FaBoPlatform/GameFive/firmware/doom/main/i_sound.c

/*
 * Game Five DOOM — sound layer: 8-channel SFX mixer + OPL2 music
 * -> MAX98357A over I2S
 *
 * PrBoom: Copyright (C) 1999-2006 id Software, Lee Killough, Colin Phipps
 * et al., GPL-2.0. Game Five I2S implementation 2026.
 *
 * SFX: DMX-format lumps are read zero-copy from the memory-mapped WAD
 * partition and resampled by a 16.16 stepper into the mix.
 * Music: MUS lump -> MIDI (mus2mid) -> prboom-plus opl_synth_player
 * (DBOPL OPL2 emulator, components/oplmusic) rendered synchronously in
 * the same mixer task on core 1.
 *
 * The I2S LRCLK MUST be a MAX98357A-supported rate (8/16/32/44.1/48 kHz).
 * 11025 Hz is NOT in the amp's supported list — its clock monitor mutes
 * the output entirely (this was why the first revision made no sound).
 * We run everything at 32 kHz and let the steppers resample.
 */

#include "config.h"
#include <string.h>
#include <stdio.h>
#include <stdlib.h>
#include "doomdef.h"
#include "doomstat.h"
#include "doomtype.h"
#include "sounds.h"
#include "s_sound.h"
#include "i_sound.h"
#include "w_wad.h"
#include "lprintf.h"
#include "memio.h"
#include "mus2mid.h"
#include "musicplayer.h"

#include "freertos/FreeRTOS.h"
#include "freertos/task.h"
#include "freertos/semphr.h"
#include "driver/i2s_std.h"
#include "esp_cpu.h"

#include "doom_config.h"

extern const music_player_t opl_synth_player;

int snd_card = 1;        /* sfx enabled */
int mus_card = 1;        /* OPL2 music */
int snd_samplerate = 32000;
int mus_opl_gain = 50;   /* used by oplmusic/opl.c FillBuffer */

#define MIX_RATE     32000        /* MAX98357A-supported LRCLK */
#define MIX_FRAMES   256          /* 8 ms per block at 32 kHz */
#define NUM_CHANNELS 16
#define MASTER_SHIFT 2            /* s(-128..127)*vol(0..127)>>2 ≈ -12dBFS/ch */

typedef struct {
    const uint8_t *data;   /* unsigned 8-bit samples (mmapped flash) */
    uint32_t len;          /* sample count */
    uint32_t pos;          /* 16.16 fixed */
    uint32_t step;         /* 16.16 fixed: lump rate / MIX_RATE */
    int vol;               /* 0..127 */
    volatile int active;
} mix_chan_t;

static mix_chan_t chans[NUM_CHANNELS];
static portMUX_TYPE snd_mux = portMUX_INITIALIZER_UNLOCKED;
static i2s_chan_handle_t s_tx;
static int snd_inited;

/* ---- music state (guarded by mus_lock: API calls come from the doom
 * task on core 0, rendering happens in the sound task on core 1) ---- */
static SemaphoreHandle_t mus_lock;
static int mus_inited;
static const void *mus_handle;
static void *mus_mididata;         /* converted MIDI buffer (heap) */
static volatile int mus_playing;

static void sound_task(void *arg)
{
    static int16_t buf[MIX_FRAMES * 2];  /* L+R interleaved */
    static int16_t mbuf[MIX_FRAMES * 2]; /* music render block */
    uint32_t prof_cycles = 0, prof_blocks = 0;

    for (;;) {
        uint32_t c0 = esp_cpu_get_cycle_count();

        /* music first: OPL render into its own block */
        int have_music = 0;
        if (mus_inited && xSemaphoreTake(mus_lock, 0) == pdTRUE) {
            if (mus_playing) {
                opl_synth_player.render(mbuf, MIX_FRAMES);
                have_music = 1;
            }
            xSemaphoreGive(mus_lock);
        }

        for (int i = 0; i < MIX_FRAMES; i++) {
            int32_t mix = have_music ? mbuf[i * 2] : 0;
            taskENTER_CRITICAL(&snd_mux);
            for (int c = 0; c < NUM_CHANNELS; c++) {
                mix_chan_t *ch = &chans[c];
                if (!ch->active)
                    continue;
                uint32_t idx = ch->pos >> 16;
                if (idx >= ch->len) {
                    ch->active = 0;
                    continue;
                }
                mix += (((int)ch->data[idx] - 128) * ch->vol) >> MASTER_SHIFT;
                ch->pos += ch->step;
            }
            taskEXIT_CRITICAL(&snd_mux);
            if (mix > 32767) mix = 32767;
            if (mix < -32768) mix = -32768;
            buf[i * 2] = (int16_t)mix;
            buf[i * 2 + 1] = (int16_t)mix;
        }

        prof_cycles += esp_cpu_get_cycle_count() - c0;
        if (++prof_blocks == 1250) {   /* ~10 s of blocks */
            /* budget per block: 8 ms * 240 MHz = 1.92 Mcycles */
            lprintf(LO_INFO, "sound_task: avg %u cyc/block (budget 1920000)\n",
                    (unsigned)(prof_cycles / prof_blocks));
            prof_cycles = prof_blocks = 0;
        }

        size_t written;
        esp_err_t err =
            i2s_channel_write(s_tx, buf, sizeof(buf), &written, portMAX_DELAY);
        static int dbg_state; /* 0=init, 1=reported nonzero, <0=reported err */
        if (err != ESP_OK && dbg_state >= 0) {
            dbg_state = -1;
            lprintf(LO_WARN, "sound_task: i2s write err 0x%x\n", err);
        } else if (dbg_state == 0 && buf[0] != 0) {
            dbg_state = 1;
            lprintf(LO_INFO, "sound_task: first nonzero audio block\n");
        }
    }
}

void I_InitSound(void)
{
    if (snd_inited)
        return;

    i2s_chan_config_t ccfg =
        I2S_CHANNEL_DEFAULT_CONFIG(I2S_NUM_AUTO, I2S_ROLE_MASTER);
    if (i2s_new_channel(&ccfg, &s_tx, NULL) != ESP_OK) {
        lprintf(LO_WARN, "I_InitSound: i2s channel alloc failed\n");
        snd_card = 0;
        mus_card = 0;
        return;
    }
    i2s_std_config_t scfg = {
        .clk_cfg = I2S_STD_CLK_DEFAULT_CONFIG(MIX_RATE),
        .slot_cfg = I2S_STD_PHILIPS_SLOT_DEFAULT_CONFIG(
            I2S_DATA_BIT_WIDTH_16BIT, I2S_SLOT_MODE_STEREO),
        .gpio_cfg = {
            .mclk = I2S_GPIO_UNUSED,
            .bclk = 6,   /* GF_PIN_I2S_BCLK  (XIAO D5) */
            .ws   = 43,  /* GF_PIN_I2S_LRCLK (XIAO D6) */
            .dout = 44,  /* GF_PIN_I2S_DIN   (XIAO D7) */
            .din  = I2S_GPIO_UNUSED,
        },
    };
    if (i2s_channel_init_std_mode(s_tx, &scfg) != ESP_OK ||
        i2s_channel_enable(s_tx) != ESP_OK) {
        lprintf(LO_WARN, "I_InitSound: i2s init failed\n");
        snd_card = 0;
        mus_card = 0;
        return;
    }

    mus_lock = xSemaphoreCreateMutex();
    I_InitMusic();

    xTaskCreatePinnedToCore(sound_task, "sound", 8192, NULL, 6, NULL, 1);
    snd_inited = 1;
    lprintf(LO_INFO, "I_InitSound: I2S %d Hz, %d mix channels, music=%s\n",
            MIX_RATE, NUM_CHANNELS, mus_inited ? "OPL2" : "off");
}

void I_ShutdownSound(void)
{
}

void I_SetChannels(void)
{
}

int I_GetSfxLumpNum(sfxinfo_t *sfx)
{
    char namebuf[9];
    snprintf(namebuf, sizeof(namebuf), "ds%.6s", sfx->name);
    return W_CheckNumForName(namebuf);
}

/*
 * DMX lump: u16 format(=3), u16 rate, u32 length, then `length` unsigned
 * 8-bit samples of which the first/last 16 are padding.
 */
int I_StartSound(int id, int channel, int vol, int sep, int pitch,
                 int priority)
{
    if (!snd_inited || channel < 0 || channel >= NUM_CHANNELS)
        return -1;

    sfxinfo_t *sfx = &S_sfx[id];
    if (sfx->lumpnum < 0)
        sfx->lumpnum = I_GetSfxLumpNum(sfx);
    if (sfx->lumpnum < 0)
        return -1;

    const uint8_t *lump = W_CacheLumpNum(sfx->lumpnum);
    int lumplen = W_LumpLength(sfx->lumpnum);
    if (lump == NULL || lumplen < 8 + 32) {
        if (lump) W_UnlockLumpNum(sfx->lumpnum);
        return -1;
    }

    uint16_t fmt = lump[0] | (lump[1] << 8);
    uint16_t rate = lump[2] | (lump[3] << 8);
    uint32_t dlen = lump[4] | (lump[5] << 8) | (lump[6] << 16)
                    | ((uint32_t)lump[7] << 24);
    if (fmt != 3 || rate == 0) {
        W_UnlockLumpNum(sfx->lumpnum);
        return -1;
    }
    if (dlen > (uint32_t)(lumplen - 8))
        dlen = lumplen - 8;
    if (dlen <= 32) {
        W_UnlockLumpNum(sfx->lumpnum);
        return -1;
    }

    taskENTER_CRITICAL(&snd_mux);
    chans[channel].active = 0;
    chans[channel].data = lump + 8 + 16;   /* skip header + lead-in pad */
    chans[channel].len = dlen - 32;        /* drop both pads */
    chans[channel].pos = 0;
    chans[channel].step = ((uint32_t)rate << 16) / MIX_RATE;
    chans[channel].vol = vol < 0 ? 0 : (vol > 127 ? 127 : vol);
    chans[channel].active = 1;
    taskEXIT_CRITICAL(&snd_mux);

    static int dbg_count;
    if (dbg_count < 5) {
        dbg_count++;
        lprintf(LO_INFO, "I_StartSound: ds%.6s ch=%d vol=%d rate=%u len=%u\n",
                sfx->name, channel, vol, rate, (unsigned)(dlen - 32));
    }

    /* whole-partition mmap: the pointer stays valid after unlock */
    W_UnlockLumpNum(sfx->lumpnum);
    return channel;
}

void I_StopSound(int handle)
{
    if (handle < 0 || handle >= NUM_CHANNELS)
        return;
    taskENTER_CRITICAL(&snd_mux);
    chans[handle].active = 0;
    taskEXIT_CRITICAL(&snd_mux);
}

int I_SoundIsPlaying(int handle)
{
    if (handle < 0 || handle >= NUM_CHANNELS)
        return 0;
    return chans[handle].active != 0;
}

int I_AnySoundStillPlaying(void)
{
    for (int c = 0; c < NUM_CHANNELS; c++)
        if (chans[c].active)
            return 1;
    return 0;
}

void I_UpdateSoundParams(int handle, int volume, int seperation, int pitch)
{
    if (handle < 0 || handle >= NUM_CHANNELS)
        return;
    taskENTER_CRITICAL(&snd_mux);
    chans[handle].vol = volume < 0 ? 0 : (volume > 127 ? 127 : volume);
    taskEXIT_CRITICAL(&snd_mux);
}

/* ---- music: prboom-plus OPL2 synth (components/oplmusic) ---- */

void I_InitMusic(void)
{
    if (mus_inited || !mus_card)
        return;
    if (opl_synth_player.init(MIX_RATE)) {
        mus_inited = 1;
        lprintf(LO_INFO, "I_InitMusic: %s at %d Hz\n",
                opl_synth_player.name(), MIX_RATE);
    } else {
        mus_card = 0;
        lprintf(LO_WARN, "I_InitMusic: OPL init failed, music off\n");
    }
}

void I_ShutdownMusic(void)
{
}

/*
 * prboom hands us the raw lump (usually MUS, sometimes already MIDI).
 * Convert MUS -> standard MIDI in a heap buffer that must outlive the
 * song (the player parses it lazily); free it in I_UnRegisterSong.
 */
int I_RegisterSong(const void *data, size_t len)
{
    if (!mus_inited || data == NULL || len < 4)
        return 0;

    const void *mididata = data;
    size_t midilen = len;
    void *converted = NULL;

    if (memcmp(data, "MUS\x1a", 4) == 0) {
        MEMFILE *in = mem_fopen_read(data, len);
        MEMFILE *out = mem_fopen_write();
        if (in == NULL || out == NULL || mus2mid(in, out)) {
            lprintf(LO_WARN, "I_RegisterSong: MUS->MIDI conversion failed\n");
            if (in) mem_fclose(in);
            if (out) mem_fclose(out);
            return 0;
        }
        void *outbuf;
        size_t outlen;
        mem_get_buf(out, &outbuf, &outlen);
        converted = malloc(outlen);
        if (converted == NULL) {
            mem_fclose(in);
            mem_fclose(out);
            return 0;
        }
        memcpy(converted, outbuf, outlen);
        mididata = converted;
        midilen = outlen;
        mem_fclose(in);
        mem_fclose(out);
    }

    xSemaphoreTake(mus_lock, portMAX_DELAY);
    if (mus_handle) {                       /* stale song still registered */
        opl_synth_player.stop();
        opl_synth_player.unregistersong(mus_handle);
        mus_handle = NULL;
        free(mus_mididata);
        mus_mididata = NULL;
        mus_playing = 0;
    }
    mus_handle = opl_synth_player.registersong(mididata, midilen);
    if (mus_handle)
        mus_mididata = converted;           /* may be NULL for raw MIDI */
    xSemaphoreGive(mus_lock);

    if (mus_handle == NULL) {
        free(converted);
        lprintf(LO_WARN, "I_RegisterSong: registersong failed\n");
        return 0;
    }
    return 1;
}

void I_PlaySong(int handle, int looping)
{
    if (!mus_inited)
        return;
    xSemaphoreTake(mus_lock, portMAX_DELAY);
    if (mus_handle) {
        opl_synth_player.play(mus_handle, looping);
        mus_playing = 1;
    }
    xSemaphoreGive(mus_lock);
    static int dbg_music;
    if (dbg_music < 3) {
        dbg_music++;
        lprintf(LO_INFO, "I_PlaySong: looping=%d\n", looping);
    }
}

void I_PauseSong(int handle)
{
    if (!mus_inited)
        return;
    xSemaphoreTake(mus_lock, portMAX_DELAY);
    opl_synth_player.pause();
    xSemaphoreGive(mus_lock);
}

void I_ResumeSong(int handle)
{
    if (!mus_inited)
        return;
    xSemaphoreTake(mus_lock, portMAX_DELAY);
    opl_synth_player.resume();
    xSemaphoreGive(mus_lock);
}

void I_StopSong(int handle)
{
    if (!mus_inited)
        return;
    xSemaphoreTake(mus_lock, portMAX_DELAY);
    opl_synth_player.stop();
    mus_playing = 0;
    xSemaphoreGive(mus_lock);
}

void I_UnRegisterSong(int handle)
{
    if (!mus_inited)
        return;
    xSemaphoreTake(mus_lock, portMAX_DELAY);
    if (mus_handle) {
        opl_synth_player.stop();
        opl_synth_player.unregistersong(mus_handle);
        mus_handle = NULL;
        free(mus_mididata);
        mus_mididata = NULL;
        mus_playing = 0;
    }
    xSemaphoreGive(mus_lock);
}

int I_RegisterMusic(const char *filename, musicinfo_t *song)
{
    return 1;  /* no filesystem music */
}

void I_SetMusicVolume(int volume)
{
    if (!mus_inited)
        return;
    xSemaphoreTake(mus_lock, portMAX_DELAY);
    opl_synth_player.setvolume(volume);   /* both use the 0..15 scale */
    xSemaphoreGive(mus_lock);
}
